kaisersuzuki/binaural-goggle/hardware/pcb/images/3.JPG

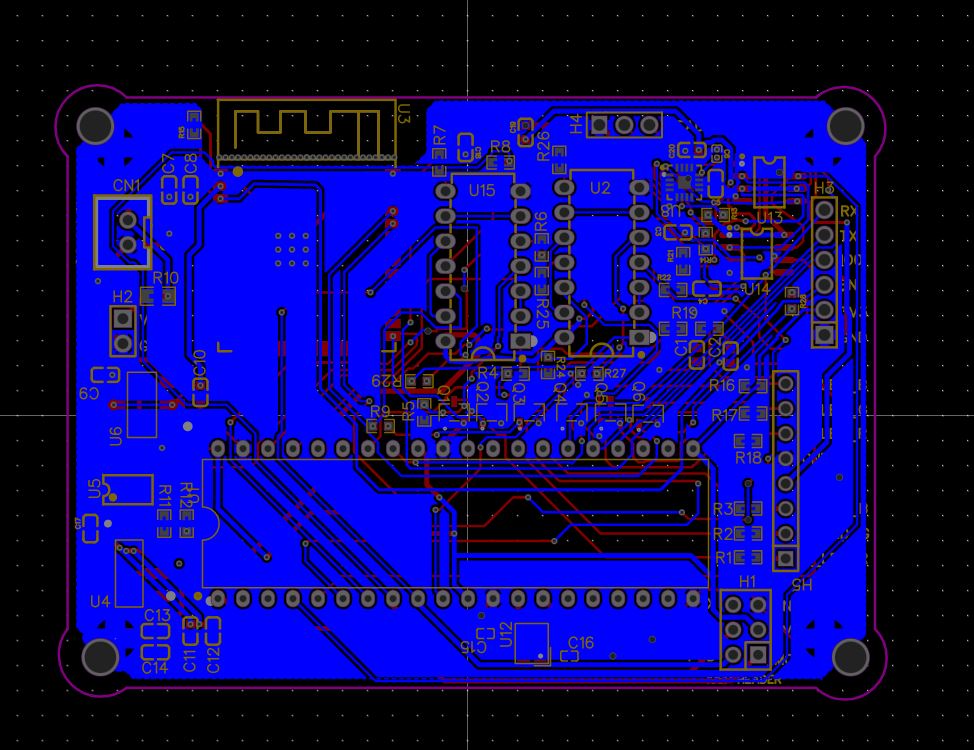
hardware/pcb/images/3.JPG
