kaisersuzuki/binaural-goggle/hardware/pcb/images/4.JPG

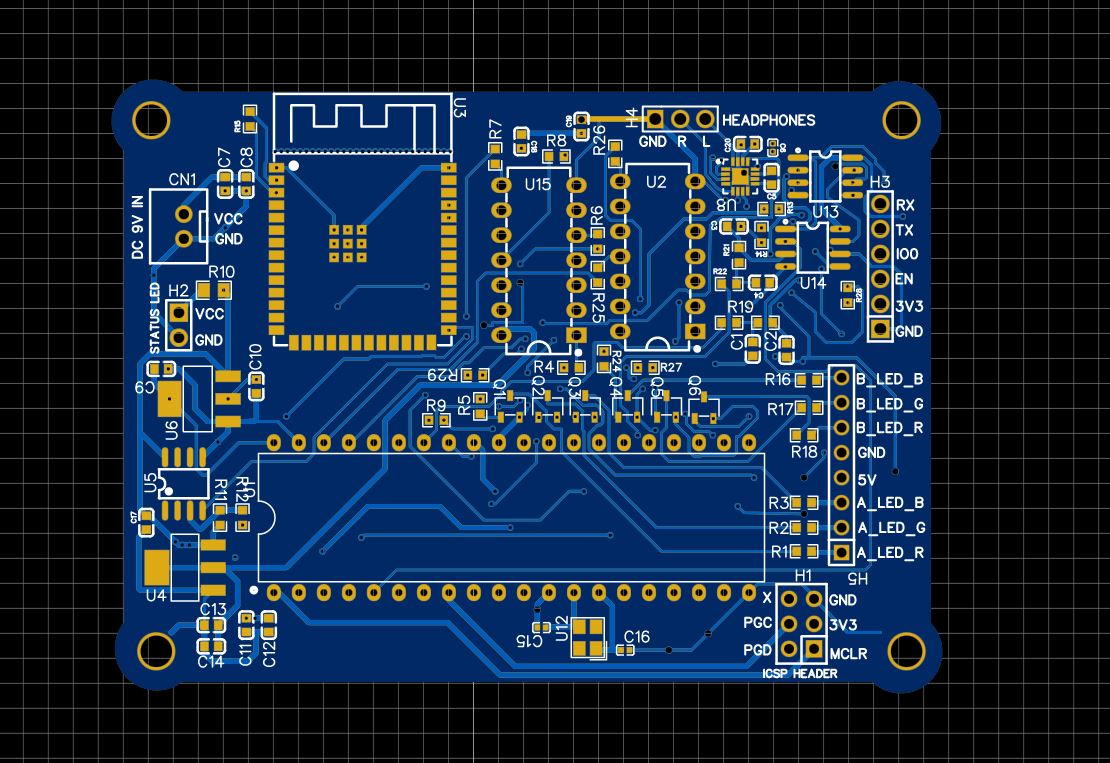
hardware/pcb/images/4.JPG
