kaisersuzuki/binaural-goggle/hardware/pcb/images/5.JPG

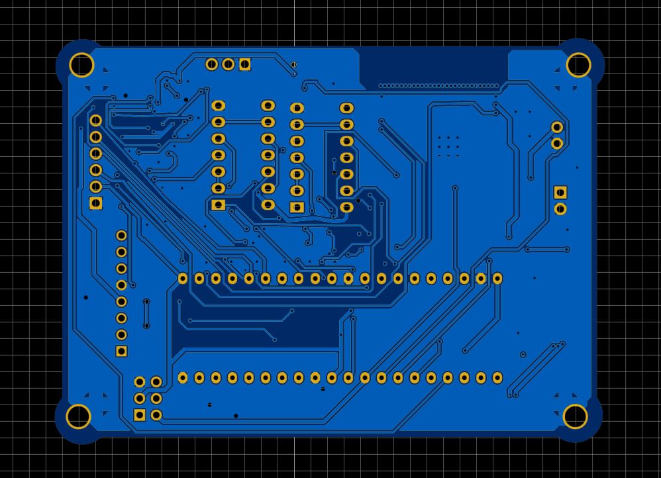
hardware/pcb/images/5.JPG
