kaisersuzuki/binaural-goggle/hardware/pcb/images/6.JPG

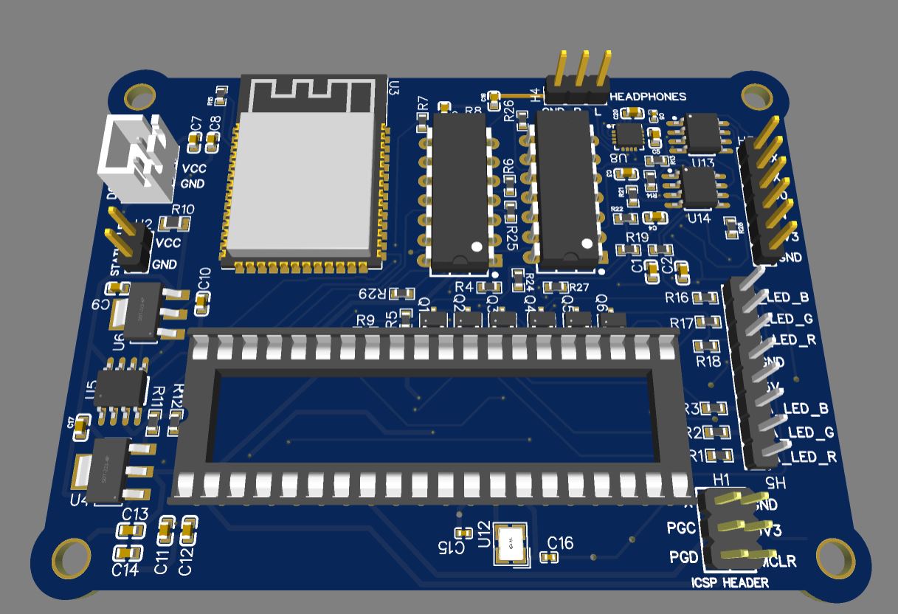
hardware/pcb/images/6.JPG
