kaisersuzuki/binaural-goggle/hardware/pcb/images/7.JPG

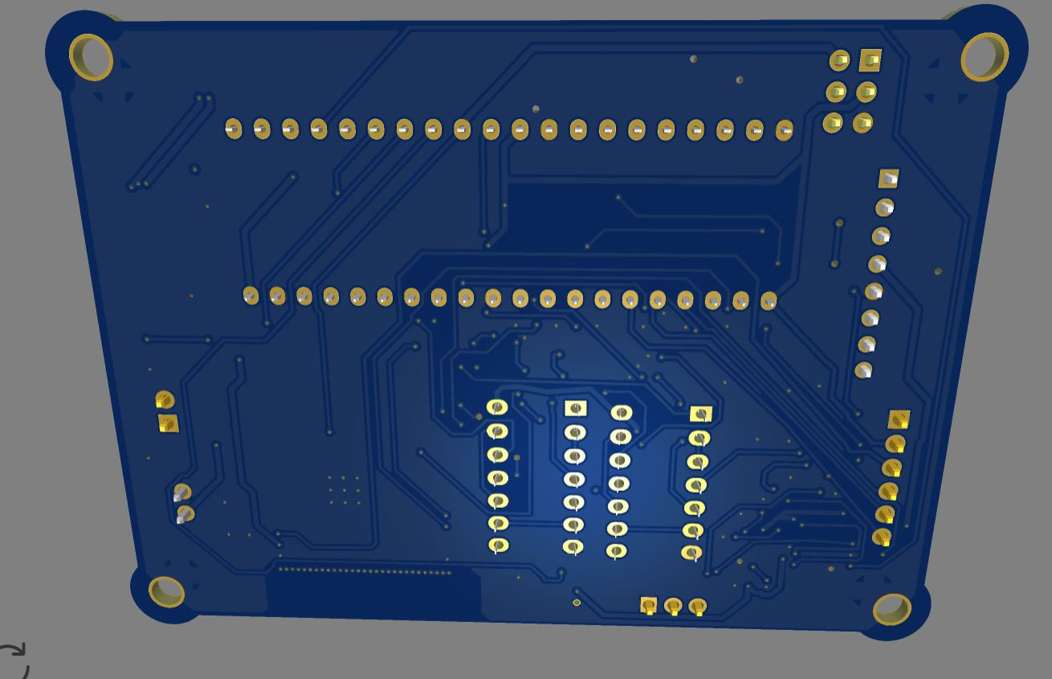
hardware/pcb/images/7.JPG
