kaisersuzuki/binaural-goggle/hardware/pcb/images/8.JPG

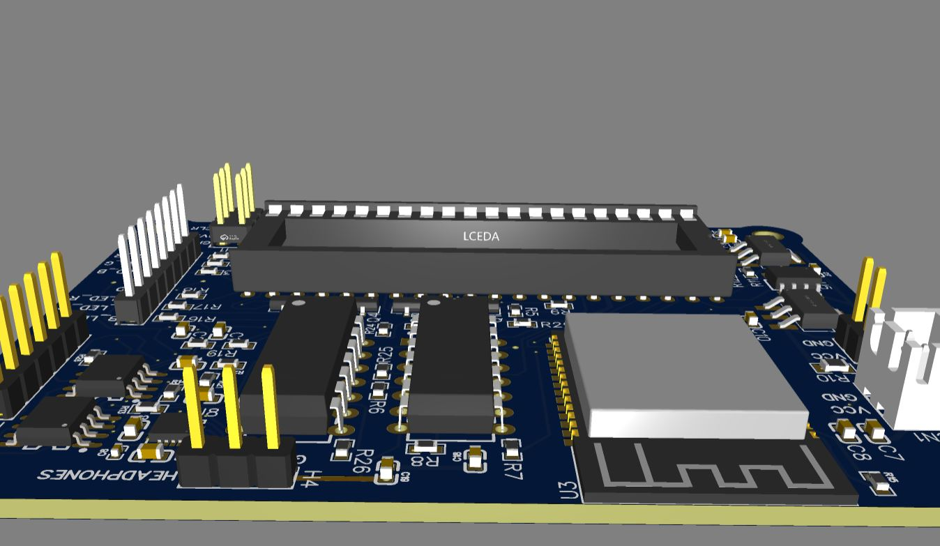
hardware/pcb/images/8.JPG
