kaisersuzuki/binaural-goggle/hardware/pcb/images/9.JPG

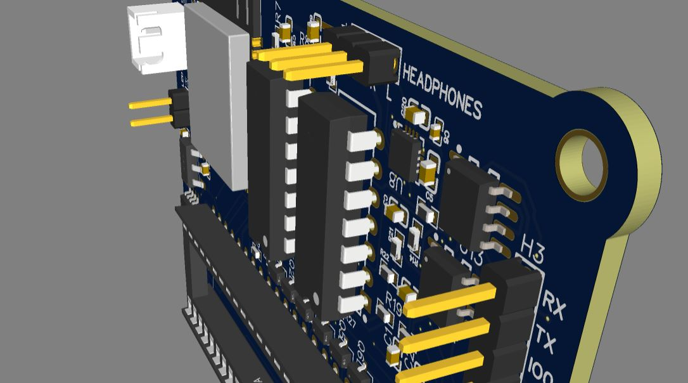
hardware/pcb/images/9.JPG
